kyo-ta04/Pico2ROMEmuCB/IMG/Pico2ROMEmuCB_sch_3.jpg

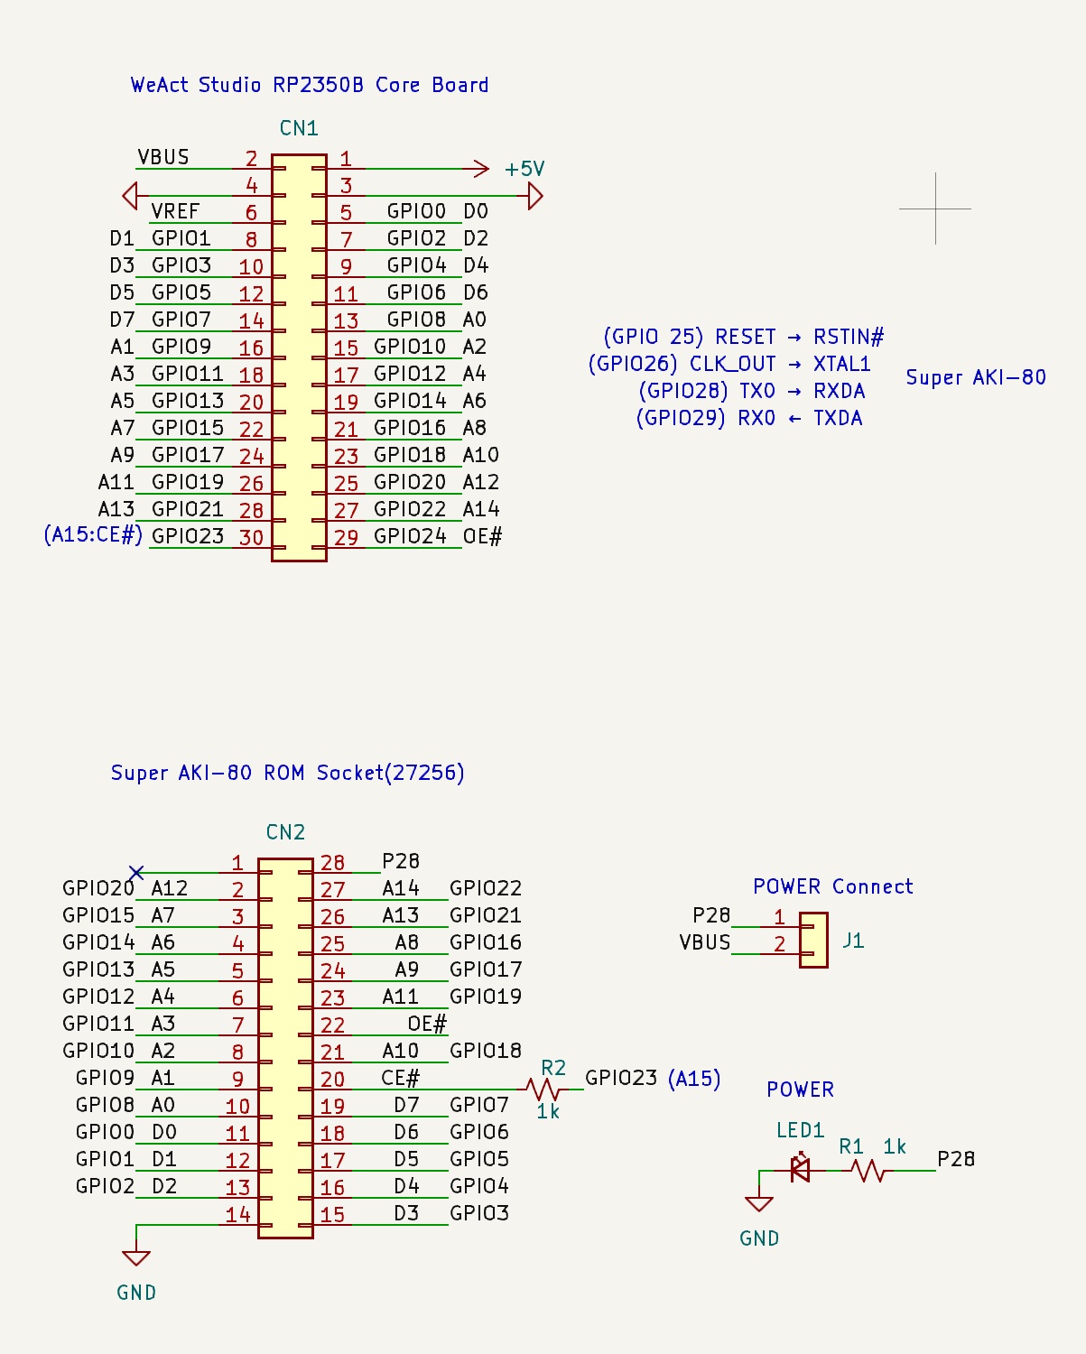
IMG/Pico2ROMEmuCB_sch_3.jpg
