kyo-ta04/Pico2ROMEmuCB/saki80mon041_const.c

const unsigned char rom_saki80mon041[32768] = {
  0xC3, 0xAE, 0x00, 0xC3, 0x42, 0x01, 0x00, 0x00, 0xC3, 0xC2, 0x2D, 0x00, 0x00, 0x00, 0x00, 0x00, // 0x0000
  0xC3, 0x95, 0x2D, 0x00, 0x00, 0x00, 0x00, 0x00, 0xC3, 0xBD, 0x2D, 0x00, 0x00, 0x00, 0x00, 0x00, // 0x0010
  0xC9, 0x00, 0x00, 0x00, 0x00, 0x00, 0x00, 0x00, 0xC9, 0x00, 0x00, 0x00, 0x00, 0x00, 0x00, 0x00, // 0x0020
  0xC3, 0xAC, 0x26, 0x00, 0x00, 0x00, 0x00, 0x00, 0xC3, 0x39, 0x27, 0x00, 0x00, 0x00, 0x00, 0x00, // 0x0030
  0x68, 0x00, 0x18, 0x04, 0x44, 0x03, 0xC1, 0x05, 0xE8, 0x01, 0x10, 0x18, 0x01, 0x00, 0x02, 0x40, // 0x0040
  0x07, 0x04, 0x00, 0x00, 0x00, 0x00, 0x00, 0x00, 0x00, 0x00, 0x00, 0x00, 0x00, 0x00, 0x00, 0x00, // 0x0050
  0x00, 0x00, 0x00, 0x00, 0x00, 0x00, 0xED, 0x45, 0xF5, 0xC5, 0xD5, 0xE5, 0xDB, 0x18, 0x57, 0x3A, // 0x0060
  0x44, 0xFF, 0xFE, 0x40, 0x28, 0x15, 0x3C, 0x32, 0x44, 0xFF, 0x3A, 0x46, 0xFF, 0x4F, 0x06, 0x00, // 0x0070
  0x21, 0x50, 0xFF, 0x09, 0x72, 0x3C, 0xE6, 0x3F, 0x32, 0x46, 0xFF, 0xE1, 0xD1, 0xC1, 0xF1, 0xFB, // 0x0080
  0xED, 0x4D, 0x21, 0x50, 0x00, 0x06, 0x02, 0x0E, 0x13, 0xED, 0xB3, 0x21, 0x42, 0x00, 0x06, 0x09, // 0x0090
  0x0E, 0x19, 0xED, 0xB3, 0x21, 0x4B, 0x00, 0x06, 0x05, 0x0E, 0x1B, 0xED, 0xB3, 0xC9, 0xF3, 0x31, // 0x00A0
  0xD0, 0xFE, 0x21, 0x00, 0x80, 0x01, 0x00, 0x80, 0xAF, 0x77, 0x23, 0x0B, 0x78, 0xB1, 0x20, 0xF8, // 0x00B0
  0xED, 0x5E, 0x21, 0x40, 0x00, 0x7C, 0xED, 0x47, 0xCD, 0x92, 0x00, 0xFB, 0x21, 0x00, 0x80, 0x22, // 0x00C0
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
  0x0D, 0x0A, 0x00, 0xD5, 0xE5, 0xCD, 0x6B, 0x02, 0xE1, 0xD1, 0xC9, 0xAF, 0x47, 0x4F, 0xCD, 0x5A, // 0x0260
  0x26, 0xB7, 0xC8, 0xCD, 0x8D, 0x02, 0xD8, 0xF5, 0x08, 0xF1, 0xCD, 0x9C, 0x02, 0xD8, 0x08, 0xE5, // 0x0270
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
};
